zeeman-effect/pixel-snap-voice/hardware/kicad/check_erc.py

#!/usr/bin/env python3
"""Retired generated-board ERC (nets.json XI/XO / J1 / U2A).

Official schematic proof is hardware/kicad/recorder/verify_schematic.py.
"""

from __future__ import annotations

import sys


def main() -> int:
    print("check_erc: retired. Run python hardware/kicad/recorder/verify_schematic.py")
    return 0


if __name__ == "__main__":
    sys.exit(main())
